veebch/photon/cases/Large Case/PXL_20221101_124922552.jpg

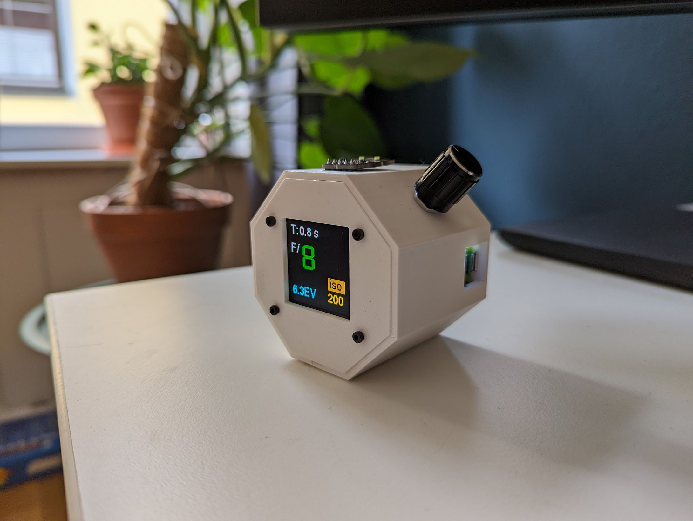
cases/Large Case/PXL_20221101_124922552.jpg
